ExploreEmbedded/hornbill-our/hornbill-our-firmware/main/ble.h

#include "bt.h" //bluetooth api
#include "bta_api.h"

#include "esp_gap_ble_api.h"
#include "esp_gatts_api.h"
#include "esp_bt_defs.h"
#include "esp_bt_main.h"
#include "esp32_rmt.h"

#ifndef HORNBILL_BLE_H_
#define HORNBILL_BLE_H_

#define GATTS_TAG                   "GATTS_DEMO"
#define GATTS_SERVICE_UUID_TEST_A   0x00FF
#define GATTS_CHAR_UUID_TEST_A      0xFF01
#define GATTS_DESCR_UUID_TEST_A     0x3333
#define GATTS_NUM_HANDLE_TEST_A     4

#define TEST_DEVICE_NAME            "Hornbill OUR"
#define TEST_MANUFACTURER_DATA_LEN  17

#define GATTS_DEMO_CHAR_VAL_LEN_MAX 0x40

#define PROFILE_NUM 1
#define PROFILE_A_APP_ID 0


void ir_Remote_task(void *param); 

void gatts_event_handler(esp_gatts_cb_event_t event, esp_gatt_if_t gatts_if, esp_ble_gatts_cb_param_t *param);
void gap_event_handler(esp_gap_ble_cb_event_t event, esp_ble_gap_cb_param_t *param);


#endif
